Nmachekhin/old_phone/code/main/SoundController.h

#pragma once
#include <PCM.h>


const unsigned char ring_sound[] PROGMEM=
{129, 127, 128, 128, 127, 129, 127, 128, 127, 128, 128, 127, 129, 127, 128, 128, 127, 129, 126, 129, 127, 128, 129, 127, 129, 127, 129, 128, 127, 129, 126, 129, 127, 127, 128, 126, 129, 126, 128, 128, 126, 129, 127, 128, 126, 128, 
129, 126, 129, 127, 128, 128, 125, 129, 125, 128, 127, 127, 129, 125, 129, 127, 128, 127, 125, 130, 125, 128, 127, 126, 130, 125, 129, 126, 127, 128, 125, 130, 125, 128, 127, 125, 129, 124, 128, 127, 127, 130, 126, 128, 125, 126, 127, 
128, 128, 123, 129, 126, 128, 130, 125, 131, 125, 126, 128, 126, 128, 123, 129, 126, 128, 130, 125, 133, 124, 127, 129, 119, 131, 129, 128, 127, 126, 128, 126, 132, 123, 126, 121, 122, 138, 118, 130, 134, 121, 142, 125, 121, 131, 114, 
127, 139, 124, 115, 125, 127, 137, 127, 109, 149, 121, 106, 142, 117, 149, 141, 106, 145, 121, 122, 137, 111, 128, 126, 131, 150, 126, 120, 135, 128, 122, 129, 110, 104, 144, 153, 128, 109, 110, 137, 146, 135, 125, 117, 136, 140, 118, 
127, 110, 101, 149, 143, 127, 137, 111, 123, 144, 111, 90, 110, 146, 147, 136, 142, 122, 119, 146, 126, 104, 118, 114, 126, 149, 125, 105, 142, 155, 141, 139, 105, 109, 136, 128, 118, 105, 124, 150, 161, 150, 125, 131, 118, 116, 121, 
98, 116, 132, 141, 154, 134, 111, 129, 149, 140, 124, 103, 117, 124, 126, 128, 117, 127, 151, 160, 135, 120, 105, 102, 127, 115, 109, 137, 145, 170, 147, 117, 119, 106, 116, 125, 132, 95, 122, 156, 132, 139, 115, 116, 135, 131, 139, 
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


class SoundController{
private:
  unsigned long silencer_timer=0;
  const int silencer_gap=1000;
  long ringthone_timer=0;
  const long ringthone_duration=3000;
  

public:
  SoundController()=default;
  void play_ring(unsigned long);
  void play_silence(unsigned long);

};
